gion86/SmartLamp/Documentation/Schematics/SmartLamp/Gerber/PNGs/SmartLamp.GTL.png

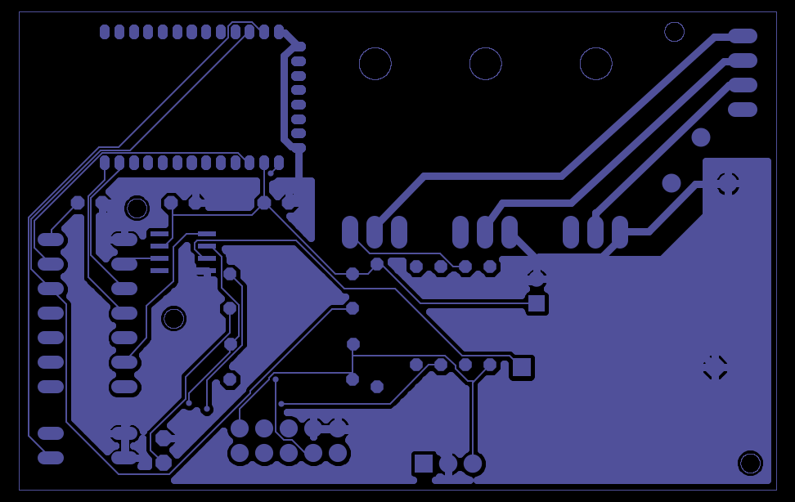
Documentation/Schematics/SmartLamp/Gerber/PNGs/SmartLamp.GTL.png
